Manims8/GroupGurd/images/product/IMG-1.jpg

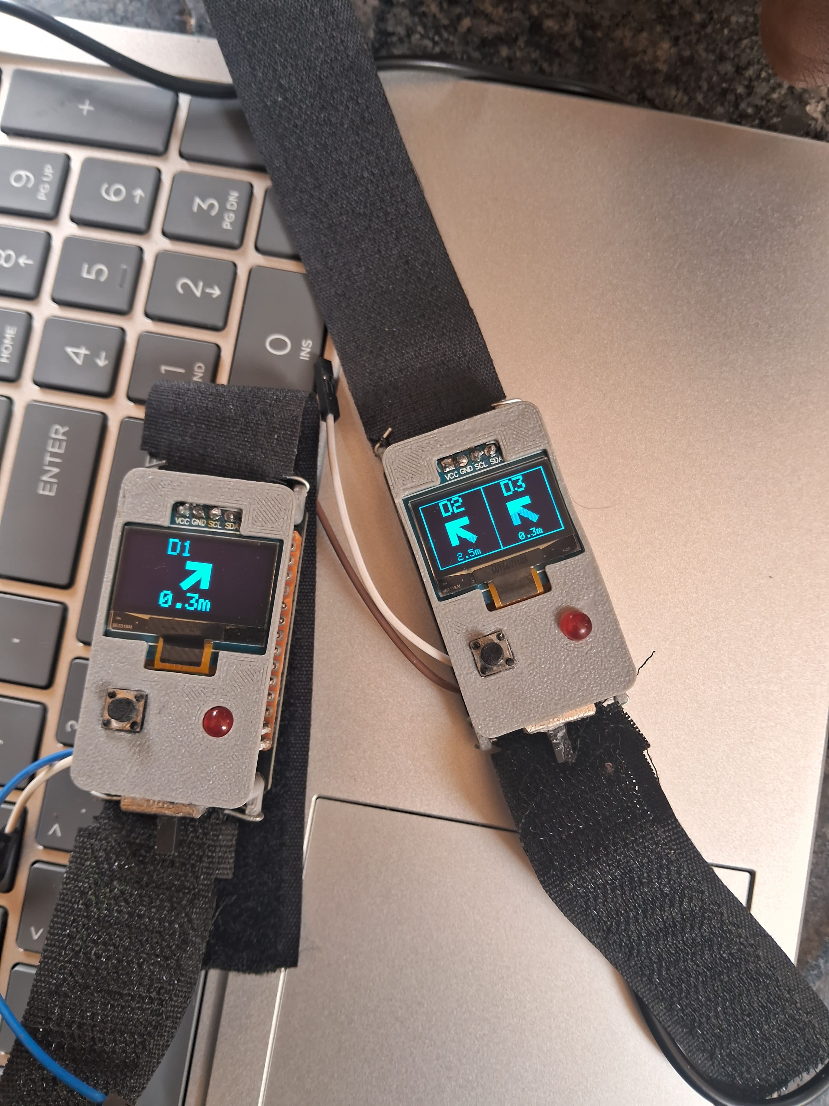
images/product/IMG-1.jpg
