Manims8/GroupGurd/images/product/IMG-2.jpg

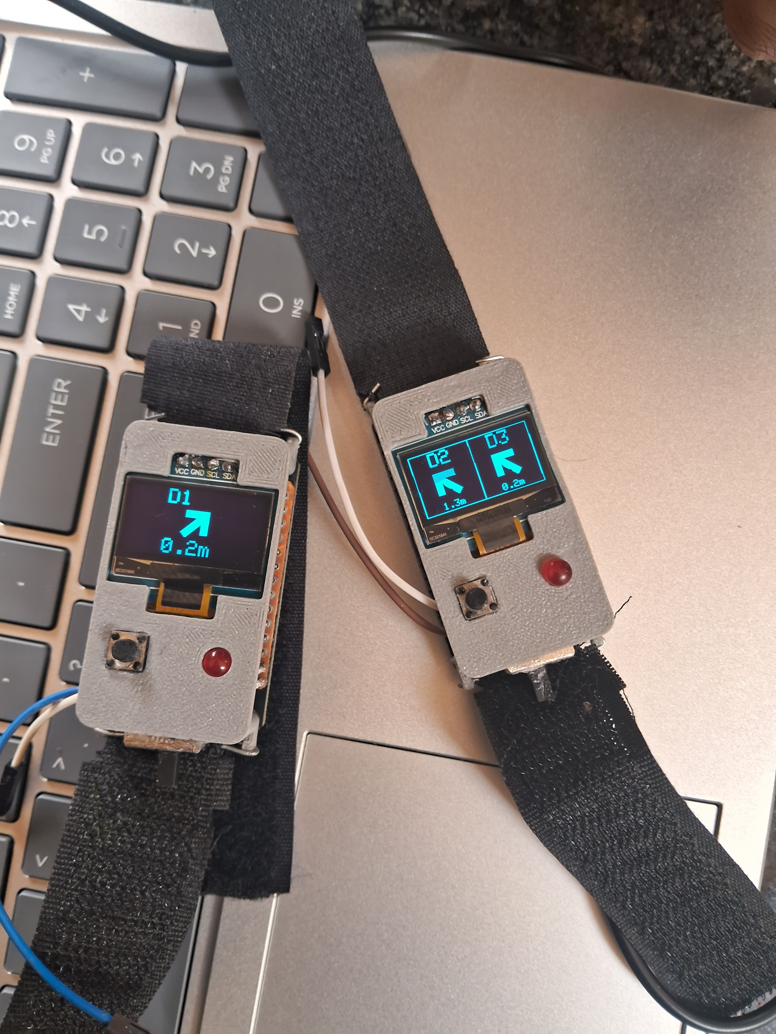
images/product/IMG-2.jpg
