Manims8/GroupGurd/images/product/IMG-3.jpg

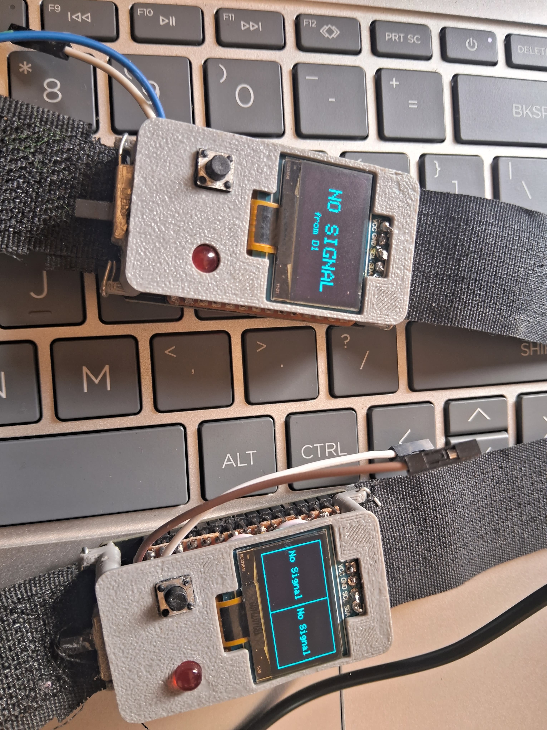
images/product/IMG-3.jpg
